robotadasufsc/Antonico-Line-Follower/Firmware/ControladorRobo/hbridge.h

#pragma once
#include "hal.h"

#define sat(x) (max(min(x,255),-255))


class HBridge
{
private:
    HBridge& operator = (HBridge& other) = delete;
    HBridge(const HBridge& other) = delete;
    HBridge();


public:
    static HBridge& self();
    enum {LEFT, RIGHT};


    void setWheelPWM(uint8_t wheel, float speed);
    void forward(int16_t vel);
};
